naorunaoru/picoarc/firmware/src/spdif.c

#include "spdif.h"

#include <stdbool.h>
#include <stdint.h>

#include "hardware/clocks.h"
#include "hardware/dma.h"
#include "hardware/pio.h"
#if PICOARC_UAC_VERSION == 2
#include "pico/critical_section.h"
#endif
#include "pico/multicore.h"
#include "pico/stdlib.h"
#include "picoarc_log.h"
#include "spdif.pio.h"

enum {
    // Each S/PDIF audio frame is 2 subframes × 32 bits × 2 half-bits = 128
    // half-bits, and the PIO outputs 1 half-bit per cycle, so the PIO clock
    // is 128× the audio sample rate (6.144 MHz at 48 kHz, 12.288 MHz at 96 kHz).
    SPDIF_HALF_BITS_PER_FRAME = 128,
    SPDIF_DEFAULT_SAMPLE_RATE_HZ = 48000,
    SPDIF_FRAMES_PER_BLOCK = 192,
    SPDIF_WORDS_PER_SUBFRAME = 2,
    SPDIF_WORDS_PER_FRAME = 4,
    SPDIF_WORDS_PER_BLOCK = SPDIF_FRAMES_PER_BLOCK * SPDIF_WORDS_PER_FRAME,
    // One slot stays empty so read == write can unambiguously mean empty.
    USB_RING_FRAMES = 2048,
#if PICOARC_UAC_VERSION == 2
    SPDIF_RATE_PPM_SCALE = 1000000,
    SPDIF_CLKDIV_Q16_SCALE = 1 << 16,
#endif
};

typedef enum {
    PREAMBLE_B,
    PREAMBLE_M,
    PREAMBLE_W,
} spdif_preamble_t;

typedef struct {
    uint16_t bits;
    uint8_t level;
    uint8_t parity;
} bmc_byte_t;

static uint32_t silence_words[SPDIF_WORDS_PER_BLOCK];
static uint32_t *build_words;
static size_t spdif_word_index;
static unsigned int current_level;
static PIO spdif_pio;
static unsigned int spdif_sm;
static unsigned int spdif_dma_chan;
static dma_channel_config spdif_dma_config;
static volatile spdif_mode_t current_mode = SPDIF_MODE_OFF;
static volatile spdif_stream_format_t current_stream_format = SPDIF_STREAM_FORMAT_PCM;
// Samples are stored 24-bit-left-aligned in int32_t (audio MSB at bit 31,
// audio LSB at bit 8). 16-bit USB input is shifted left 16 on ingest, 24-bit
// USB input is unpacked from its 3-byte little-endian form. Either way the
// S/PDIF encoder sees the same internal representation.
static int32_t usb_ring[USB_RING_FRAMES][2];
static volatile unsigned int usb_ring_read;
static volatile unsigned int usb_ring_write;
static volatile unsigned int usb_underrun_frames;
static volatile unsigned int usb_high_water_frames;
static volatile unsigned int usb_low_water_frames;
static volatile unsigned int spdif_dma_late_blocks;
static bmc_byte_t bmc_byte[2][256];
static uint8_t bmc_tail[2][2][8];
static uint32_t dma_words[2][SPDIF_WORDS_PER_BLOCK];
#if PICOARC_UAC_VERSION == 2
static volatile uint32_t adaptive_clkdiv_q16;
static volatile uint32_t adaptive_clock_generation;
static volatile bool adaptive_clock_enabled;
static uint32_t adaptive_sample_rate_hz = SPDIF_DEFAULT_SAMPLE_RATE_HZ;
static volatile unsigned int adaptive_buffered_frames_snapshot;
static volatile bool adaptive_buffered_frames_valid;
static critical_section_t adaptive_clock_critical_section;
#endif

static unsigned int buffered_frames_from(unsigned int read, unsigned int write) {
    if (write >= read) {
        return write - read;
    }

    return USB_RING_FRAMES - read + write;
}

static void build_bmc_tables(void) {
    for (unsigned int start_level = 0; start_level < 2; start_level++) {
        for (unsigned int value = 0; value < 256; value++) {
            unsigned int level = start_level;
            uint16_t bits = 0;
            unsigned int parity = 0;

            for (unsigned int bit = 0; bit < 8; bit++) {
                const bool bit_value = (value >> bit) & 1u;
                parity ^= bit_value ? 1u : 0u;

                level ^= 1u;
                if (level) {
                    bits |= 1u << (bit * 2);
                }

                if (bit_value) {
                    level ^= 1u;
                }
                if (level) {
                    bits |= 1u << (bit * 2 + 1);
                }
            }

            bmc_byte[start_level][value] = (bmc_byte_t){
                .bits = bits,
                .level = (uint8_t)level,
                .parity = (uint8_t)parity,
            };
        }
    }

    for (unsigned int start_level = 0; start_level < 2; start_level++) {
        for (unsigned int payload_parity = 0; payload_parity < 2; payload_parity++) {
            for (unsigned int vuc_bits = 0; vuc_bits < 8; vuc_bits++) {
                unsigned int level = start_level;
                unsigned int parity = payload_parity;
                uint8_t bits = 0;

                for (unsigned int bit = 0; bit < 3; bit++) {
                    const bool value = (vuc_bits >> bit) & 1u;
                    parity ^= value ? 1u : 0u;

                    level ^= 1u;
                    if (level) {
                        bits |= 1u << (bit * 2);
                    }

                    if (value) {
                        level ^= 1u;
                    }
                    if (level) {
                        bits |= 1u << (bit * 2 + 1);
                    }
                }

                const bool parity_bit = (parity & 1u) != 0;
                level ^= 1u;
                if (level) {
                    bits |= 1u << 6;
                }

                if (parity_bit) {
                    level ^= 1u;
                }
                if (level) {
                    bits |= 1u << 7;
                }

                bmc_tail[start_level][payload_parity][vuc_bits] = bits;
            }
        }
    }
}

static void append_half_bit(unsigned int level) {
    if (level) {
        build_words[spdif_word_index / 32] |= 1u << (spdif_word_index % 32);
    }
    spdif_word_index++;
}

static void append_preamble(spdif_preamble_t preamble) {
    uint8_t pattern = 0;

    switch (preamble) {
    case PREAMBLE_B:
        pattern = 0xe8;
        break;
    case PREAMBLE_M:
        pattern = 0xe2;
        break;
    case PREAMBLE_W:
        pattern = 0xe4;
        break;
    }

    if (current_level) {
        pattern = (uint8_t)~pattern;
    }

    for (int bit = 7; bit >= 0; bit--) {
        current_level = (pattern >> bit) & 1u;
        append_half_bit(current_level);
    }
}

static void append_bmc_bit(bool bit) {
    current_level ^= 1u;
    append_half_bit(current_level);

    if (bit) {
        current_level ^= 1u;
    }
    append_half_bit(current_level);
}

static void append_subframe(spdif_preamble_t preamble, int32_t sample, bool channel_status) {
    // sample is 24-bit left-aligned in int32_t; bits 31..8 carry the audio,
    // bits 7..0 are ignored. The S/PDIF subframe carries audio bits LSB-first.
    uint32_t payload = ((uint32_t)sample) >> 8;
    unsigned int ones = 0;

    append_preamble(preamble);

    for (int bit = 0; bit < 24; bit++) {
        const bool value = (payload >> bit) & 1u;
        ones += value ? 1u : 0u;
        append_bmc_bit(value);
    }

    // V and U are zero. C carries channel status, bit-by-bit across the
    // 192-frame block.
    append_bmc_bit(false);
    append_bmc_bit(false);
    append_bmc_bit(channel_status);
    ones += channel_status ? 1u : 0u;

    append_bmc_bit((ones & 1u) != 0);
}

static inline void put_bits16(uint32_t *lo, uint32_t *hi, unsigned int offset, uint16_t bits) {
    if (offset < 32) {
        *lo |= (uint32_t)bits << offset;
        if (offset > 16) {
            *hi |= (uint32_t)bits >> (32 - offset);
        }
    } else {
        *hi |= (uint32_t)bits << (offset - 32);
    }
}

static void encode_subframe_fast(uint32_t words[SPDIF_WORDS_PER_SUBFRAME],
                                 spdif_preamble_t preamble, int32_t sample,
                                 bool channel_status, unsigned int *level) {
    uint8_t pattern = 0;
    uint32_t lo = 0;
    uint32_t hi = 0;

    switch (preamble) {
    case PREAMBLE_B:
        pattern = 0xe8;
        break;
    case PREAMBLE_M:
        pattern = 0xe2;
        break;
    case PREAMBLE_W:
        pattern = 0xe4;
        break;
    }

    if (*level) {
        pattern = (uint8_t)~pattern;
    }

    for (int bit = 7; bit >= 0; bit--) {
        *level = (pattern >> bit) & 1u;
        if (*level) {
            lo |= 1u << (7 - bit);
        }
    }

    // 24 audio bits, LSB-first across three encoder bytes, taken from the
    // 24-bit-left-aligned int32 (audio MSB at bit 31, audio LSB at bit 8).
    const uint32_t raw = (uint32_t)sample;
    bmc_byte_t chunk = bmc_byte[*level][(raw >> 8) & 0xffu];
    put_bits16(&lo, &hi, 8, chunk.bits);
    *level = chunk.level;
    unsigned int parity = chunk.parity;

    chunk = bmc_byte[*level][(raw >> 16) & 0xffu];
    put_bits16(&lo, &hi, 24, chunk.bits);
    *level = chunk.level;
    parity ^= chunk.parity;

    chunk = bmc_byte[*level][(raw >> 24) & 0xffu];
    put_bits16(&lo, &hi, 40, chunk.bits);
    *level = chunk.level;
    parity ^= chunk.parity;

    const unsigned int vuc_bits = channel_status ? 0x04u : 0x00u;
    hi |= (uint32_t)bmc_tail[*level][parity][vuc_bits] << 24;
    *level = (hi >> 31) & 1u;

    words[0] = lo;
    words[1] = hi;
}

static bool channel_status_bit(unsigned int frame_index, spdif_stream_format_t format) {
    // IEC 60958 consumer channel status byte 0 bit 1: 0 = linear PCM,
    // 1 = non-PCM / encoded audio. Other bits remain zero for now.
    return format == SPDIF_STREAM_FORMAT_IEC61937 && frame_index == 1;
}

static bool read_usb_frame(int32_t *left, int32_t *right) {
    const unsigned int read = usb_ring_read;

    if (read == usb_ring_write) {
        *left = 0;
        *right = 0;
        usb_underrun_frames++;
        return false;
    }

    *left = usb_ring[read][0];
    *right = usb_ring[read][1];
    usb_ring_read = (read + 1) % USB_RING_FRAMES;

    const unsigned int buffered = buffered_frames_from(usb_ring_read, usb_ring_write);
    if (buffered < usb_low_water_frames) {
        usb_low_water_frames = buffered;
    }
    return true;
}

static void encode_live_frame(uint32_t *words, unsigned int frame_index, unsigned int *level) {
    int32_t left = 0;
    int32_t right = 0;
    const bool c_bit = channel_status_bit(frame_index, current_stream_format);

    read_usb_frame(&left, &right);
    encode_subframe_fast(&words[0], frame_index == 0 ? PREAMBLE_B : PREAMBLE_M, left, c_bit, level);
    encode_subframe_fast(&words[2], PREAMBLE_W, right, c_bit, level);
}

static void copy_block(uint32_t *dst, const uint32_t *src) {
    for (size_t i = 0; i < SPDIF_WORDS_PER_BLOCK; i++) {
        dst[i] = src[i];
    }
}

static void build_dma_block(uint32_t *words, unsigned int *frame_index, unsigned int *level) {
    const spdif_mode_t mode = current_mode;

    if (mode == SPDIF_MODE_USB_AUDIO) {
        for (unsigned int frame = 0; frame < SPDIF_FRAMES_PER_BLOCK; frame++) {
            encode_live_frame(&words[frame * SPDIF_WORDS_PER_FRAME], *frame_index, level);
            *frame_index = (*frame_index + 1) % SPDIF_FRAMES_PER_BLOCK;
        }
#if PICOARC_UAC_VERSION == 2
        critical_section_enter_blocking(&adaptive_clock_critical_section);
        if (current_mode == SPDIF_MODE_USB_AUDIO) {
            adaptive_buffered_frames_snapshot = buffered_frames_from(
                usb_ring_read, usb_ring_write);
            adaptive_buffered_frames_valid = true;
        }
        critical_section_exit(&adaptive_clock_critical_section);
#endif
        return;
    }

    if (mode == SPDIF_MODE_OFF) {
        for (size_t i = 0; i < SPDIF_WORDS_PER_BLOCK; i++) {
            words[i] = 0;
        }
        return;
    }

    copy_block(words, silence_words);
}

static void start_dma_block(const uint32_t *words) {
    dma_channel_configure(spdif_dma_chan,
                          &spdif_dma_config,
                          &spdif_pio->txf[spdif_sm],
                          words,
                          SPDIF_WORDS_PER_BLOCK,
                          true);
}

#if PICOARC_UAC_VERSION == 2
static uint32_t clkdiv_q16_for_rate_adjustment(uint32_t rate_hz,
                                               int32_t adjustment_ppm) {
    const uint64_t adjusted_scale = (uint64_t)(SPDIF_RATE_PPM_SCALE +
                                                adjustment_ppm);
    const uint64_t numerator = (uint64_t)clock_get_hz(clk_sys) *
                               SPDIF_CLKDIV_Q16_SCALE *
                               SPDIF_RATE_PPM_SCALE;
    const uint64_t denominator = (uint64_t)rate_hz *
                                 SPDIF_HALF_BITS_PER_FRAME *
                                 adjusted_scale;
    return (uint32_t)((numerator + denominator / 2u) / denominator);
}

static void apply_adaptive_clock_divider(uint32_t *dither_accumulator,
                                         uint32_t *seen_generation) {
    critical_section_enter_blocking(&adaptive_clock_critical_section);
    if (!adaptive_clock_enabled) {
        critical_section_exit(&adaptive_clock_critical_section);
        return;
    }

    const uint32_t generation = adaptive_clock_generation;
    if (generation != *seen_generation) {
        *dither_accumulator = 0;
        *seen_generation = generation;
    }

    const uint32_t target_q16 = adaptive_clkdiv_q16;
    uint32_t divider_q8 = target_q16 >> 8;
    *dither_accumulator += target_q16 & 0xffu;
    if (*dither_accumulator >= 0x100u) {
        divider_q8++;
        *dither_accumulator -= 0x100u;
    }

    pio_sm_set_clkdiv_int_frac8(spdif_pio, spdif_sm,
                                divider_q8 >> 8,
                                (uint8_t)(divider_q8 & 0xffu));
    critical_section_exit(&adaptive_clock_critical_section);
}
#endif

static void build_silence_block(uint32_t *words) {
    for (size_t i = 0; i < SPDIF_WORDS_PER_BLOCK; i++) {
        words[i] = 0;
    }

    build_words = words;
    spdif_word_index = 0;
    current_level = 0;

    for (unsigned int frame = 0; frame < SPDIF_FRAMES_PER_BLOCK; frame++) {
        append_subframe(frame == 0 ? PREAMBLE_B : PREAMBLE_M, 0, false);
        append_subframe(PREAMBLE_W, 0, false);
    }
}

static void audio_core_main(void) {
    unsigned int live_frame_index = 0;
    unsigned int live_level = 0;
    unsigned int block = 0;
#if PICOARC_UAC_VERSION == 2
    uint32_t clock_dither_accumulator = 0;
    uint32_t seen_clock_generation = adaptive_clock_generation;
#endif

    build_dma_block(dma_words[block], &live_frame_index, &live_level);
    start_dma_block(dma_words[block]);
    block ^= 1u;

    while (true) {
        build_dma_block(dma_words[block], &live_frame_index, &live_level);
        if (!dma_channel_is_busy(spdif_dma_chan)) {
            spdif_dma_late_blocks++;
        }
        dma_channel_wait_for_finish_blocking(spdif_dma_chan);
#if PICOARC_UAC_VERSION == 2
        // Limit divider changes to one per 192-frame DMA cycle. The PIO FIFO
        // can still hold the tail of the previous block, so do not restart the
        // divider or claim that this is an exact wire-level block boundary.
        apply_adaptive_clock_divider(&clock_dither_accumulator,
                                     &seen_clock_generation);
#endif
        start_dma_block(dma_words[block]);
        block ^= 1u;
    }
}

void spdif_start(unsigned int pin) {
    build_bmc_tables();
    build_silence_block(silence_words);
#if PICOARC_UAC_VERSION == 2
    critical_section_init(&adaptive_clock_critical_section);
#endif

    spdif_pio = pio0;
    spdif_sm = pio_claim_unused_sm(spdif_pio, true);
    const unsigned int offset = pio_add_program(spdif_pio, &spdif_tx_program);

    pio_gpio_init(spdif_pio, pin);
    pio_sm_set_consecutive_pindirs(spdif_pio, spdif_sm, pin, 1, true);

    pio_sm_config config = spdif_tx_program_get_default_config(offset);
    sm_config_set_out_pins(&config, pin, 1);
    sm_config_set_out_shift(&config, true, true, 32);
    sm_config_set_fifo_join(&config, PIO_FIFO_JOIN_TX);
    sm_config_set_clkdiv(&config,
                         (float)clock_get_hz(clk_sys) /
                             (SPDIF_DEFAULT_SAMPLE_RATE_HZ * SPDIF_HALF_BITS_PER_FRAME));

    pio_sm_init(spdif_pio, spdif_sm, offset, &config);
    pio_sm_set_enabled(spdif_pio, spdif_sm, true);

    spdif_dma_chan = dma_claim_unused_channel(true);
    spdif_dma_config = dma_channel_get_default_config(spdif_dma_chan);
    channel_config_set_transfer_data_size(&spdif_dma_config, DMA_SIZE_32);
    channel_config_set_read_increment(&spdif_dma_config, true);
    channel_config_set_write_increment(&spdif_dma_config, false);
    channel_config_set_dreq(&spdif_dma_config, pio_get_dreq(spdif_pio, spdif_sm, true));
    channel_config_set_high_priority(&spdif_dma_config, true);

    multicore_launch_core1(audio_core_main);
}

void spdif_set_mode(spdif_mode_t mode) {
#if PICOARC_UAC_VERSION == 2
    critical_section_enter_blocking(&adaptive_clock_critical_section);
#endif
    const spdif_mode_t previous = current_mode;
    current_mode = mode;
#if PICOARC_UAC_VERSION == 2
    if (previous != mode) {
        adaptive_buffered_frames_valid = false;
    }
    critical_section_exit(&adaptive_clock_critical_section);
#endif
    if (previous != mode) {
        printf("spdif: mode +%llums %s -> %s buf=%u\n",
               (unsigned long long)(time_us_64() / 1000),
               spdif_mode_name(previous),
               spdif_mode_name(mode),
               spdif_buffered_frames());
    }
}

void spdif_set_sample_rate(uint32_t rate_hz) {
    if (!spdif_pio) {
        // Called before spdif_start() — caller booted us out of order. Drop
        // the request rather than writing into ROM at NULL+0xC8.
        return;
    }

#if PICOARC_UAC_VERSION == 2
    // Prevent core 1 from restoring the previous adaptive divider while this
    // discrete UAC2 rate transition is being programmed.
    const uint32_t nominal_clkdiv_q16 = clkdiv_q16_for_rate_adjustment(
        rate_hz, 0);
    critical_section_enter_blocking(&adaptive_clock_critical_section);
    adaptive_clock_enabled = false;
#endif
    const float divider = (float)clock_get_hz(clk_sys) /
                          (float)(rate_hz * SPDIF_HALF_BITS_PER_FRAME);
    pio_sm_set_enabled(spdif_pio, spdif_sm, false);
    pio_sm_set_clkdiv(spdif_pio, spdif_sm, divider);
    pio_sm_clkdiv_restart(spdif_pio, spdif_sm);
    pio_sm_set_enabled(spdif_pio, spdif_sm, true);
#if PICOARC_UAC_VERSION == 2
    adaptive_sample_rate_hz = rate_hz;
    adaptive_clkdiv_q16 = nominal_clkdiv_q16;
    adaptive_clock_generation++;
    critical_section_exit(&adaptive_clock_critical_section);
#endif
}

#if PICOARC_UAC_VERSION == 2
void spdif_set_rate_adjustment_ppm(int32_t adjustment_ppm) {
    if (!spdif_pio) {
        return;
    }

    // The USB-side controller currently clamps more tightly. Keep this API
    // independently bounded so a future caller cannot underflow the scale.
    if (adjustment_ppm > 10000) {
        adjustment_ppm = 10000;
    } else if (adjustment_ppm < -10000) {
        adjustment_ppm = -10000;
    }

    const uint32_t requested_clkdiv_q16 = clkdiv_q16_for_rate_adjustment(
        adaptive_sample_rate_hz, adjustment_ppm);
    critical_section_enter_blocking(&adaptive_clock_critical_section);
    adaptive_clkdiv_q16 = requested_clkdiv_q16;
    adaptive_clock_enabled = true;
    critical_section_exit(&adaptive_clock_critical_section);
}

bool spdif_adaptive_buffered_frames(unsigned int *frames) {
    bool valid = false;
    critical_section_enter_blocking(&adaptive_clock_critical_section);
    if (current_mode == SPDIF_MODE_USB_AUDIO &&
        adaptive_buffered_frames_valid) {
        *frames = adaptive_buffered_frames_snapshot;
        valid = true;
    }
    critical_section_exit(&adaptive_clock_critical_section);
    return valid;
}
#endif

spdif_mode_t spdif_get_mode(void) {
    return current_mode;
}

void spdif_set_stream_format(spdif_stream_format_t format) {
    current_stream_format = format;
}

spdif_stream_format_t spdif_get_stream_format(void) {
    return current_stream_format;
}

const char *spdif_mode_name(spdif_mode_t mode) {
    switch (mode) {
    case SPDIF_MODE_OFF:
        return "off";
    case SPDIF_MODE_SILENCE:
        return "silence";
    case SPDIF_MODE_USB_AUDIO:
        return "usb-audio";
    default:
        return "unknown";
    }
}

unsigned int spdif_write_pcm(const int32_t *samples, unsigned int frame_count) {
    unsigned int written = 0;

    for (unsigned int i = 0; i < frame_count; i++) {
        const unsigned int write = usb_ring_write;
        const unsigned int next_write = (write + 1) % USB_RING_FRAMES;

        if (next_write == usb_ring_read) {
            break;
        }

        usb_ring[write][0] = samples[i * 2];
        usb_ring[write][1] = samples[i * 2 + 1];
        usb_ring_write = next_write;
        written++;
    }

    const unsigned int buffered = spdif_buffered_frames();
    if (buffered > usb_high_water_frames) {
        usb_high_water_frames = buffered;
    }

    return written;
}

unsigned int spdif_buffered_frames(void) {
    return buffered_frames_from(usb_ring_read, usb_ring_write);
}

void spdif_clear_usb_buffer(void) {
    usb_ring_read = 0;
    usb_ring_write = 0;
    usb_underrun_frames = 0;
    usb_high_water_frames = 0;
    usb_low_water_frames = USB_RING_FRAMES;
    spdif_dma_late_blocks = 0;
#if PICOARC_UAC_VERSION == 2
    critical_section_enter_blocking(&adaptive_clock_critical_section);
    adaptive_buffered_frames_snapshot = 0;
    adaptive_buffered_frames_valid = false;
    critical_section_exit(&adaptive_clock_critical_section);
#endif
}

void spdif_take_usb_stats(spdif_usb_stats_t *stats) {
    if (!stats) {
        return;
    }

    stats->buffered_frames = spdif_buffered_frames();
    stats->high_water_frames = usb_high_water_frames;
    stats->low_water_frames = usb_low_water_frames == USB_RING_FRAMES ?
                                  stats->buffered_frames :
                                  usb_low_water_frames;
    stats->underrun_frames = usb_underrun_frames;
    stats->dma_late_blocks = spdif_dma_late_blocks;

    usb_high_water_frames = stats->buffered_frames;
    usb_low_water_frames = stats->buffered_frames;
    usb_underrun_frames = 0;
    spdif_dma_late_blocks = 0;
}
